Greg-Bm/ploopy-adept-small-btu/v2/v2-38mm-top-trackball.step

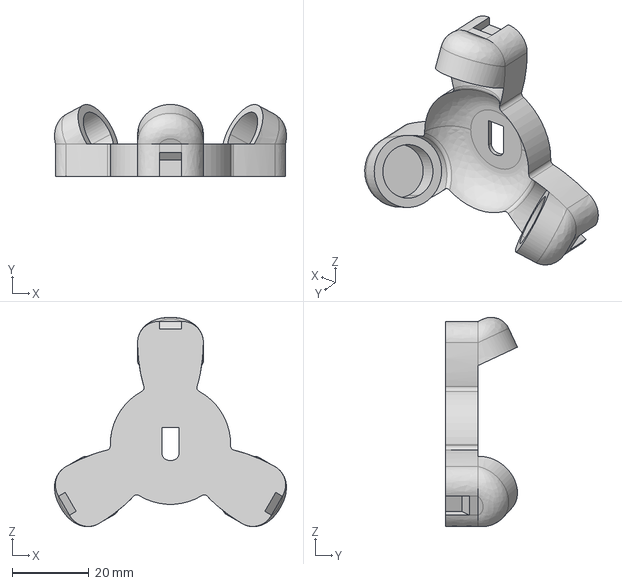
[picture p28: CAD file, 2025-01-05, an earlier design]
v2/v2-38mm-top-trackball.step
60.3 x 18.7 x 54.4 mm
