Greg-Bm/ploopy-adept-small-btu/v3/v3-bottom.step

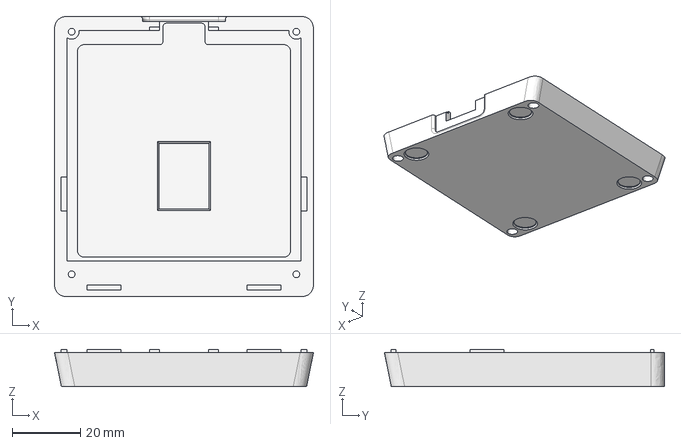
[picture p29: CAD file, 2025-04-14, an earlier design]
v3/v3-bottom.step
76.1 x 82.3 x 11.0 mm
